J7R3AN/goomerbot/Redesign goomerbot/2020_520OB.SLDPRT

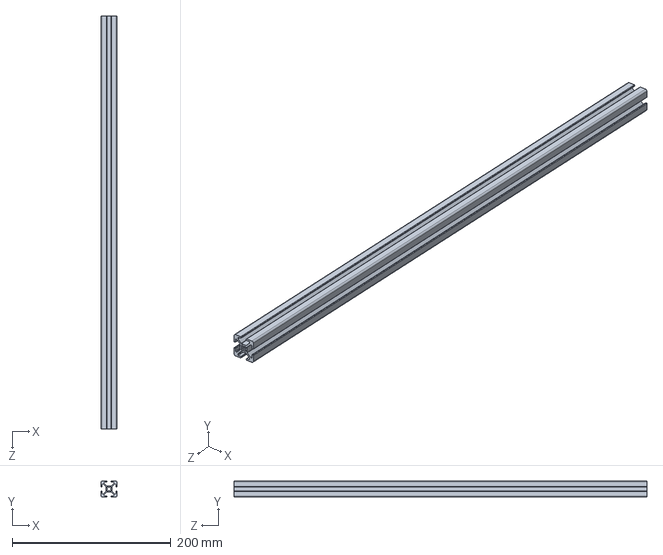
[picture p18: CAD file, 2017-09-06]
Redesign goomerbot/2020_520OB.SLDPRT
20.0 x 20.0 x 520.0 mm
