J7R3AN/goomerbot/Redesign goomerbot/2020_450OB.SLDPRT

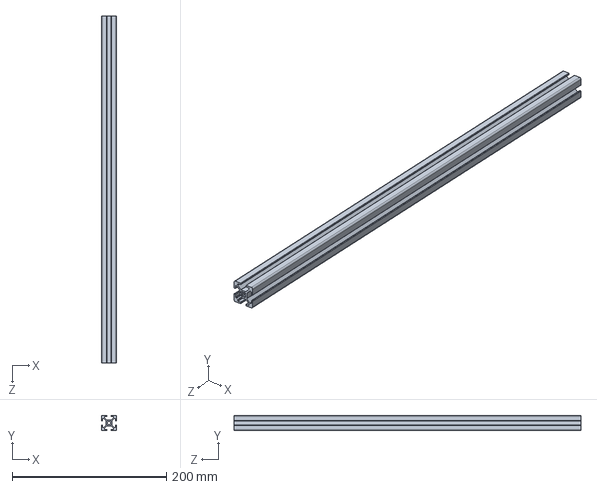
[picture p19: CAD file, 2017-09-06]
Redesign goomerbot/2020_450OB.SLDPRT
20.0 x 20.0 x 450.0 mm
