J7R3AN/goomerbot/SLDMODEL/Eje.SLDPRT

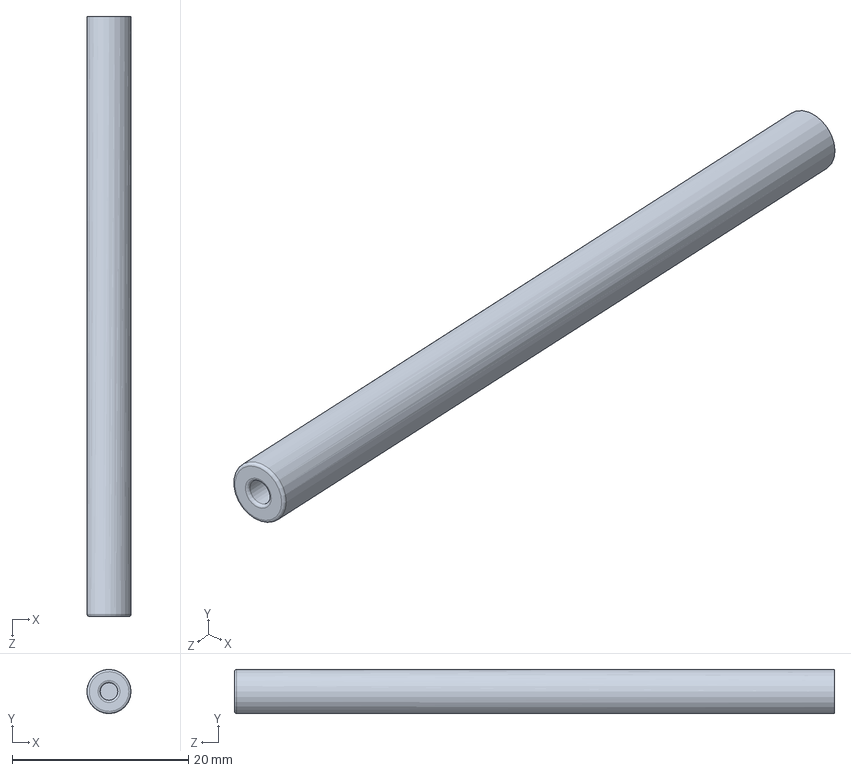
[picture p20: CAD file, 2017-03-24]
SLDMODEL/Eje.SLDPRT
5.00 x 5.00 x 68.0 mm
