J7R3AN/goomerbot/Redesign goomerbot/arduino-mega-mount.SLDPRT

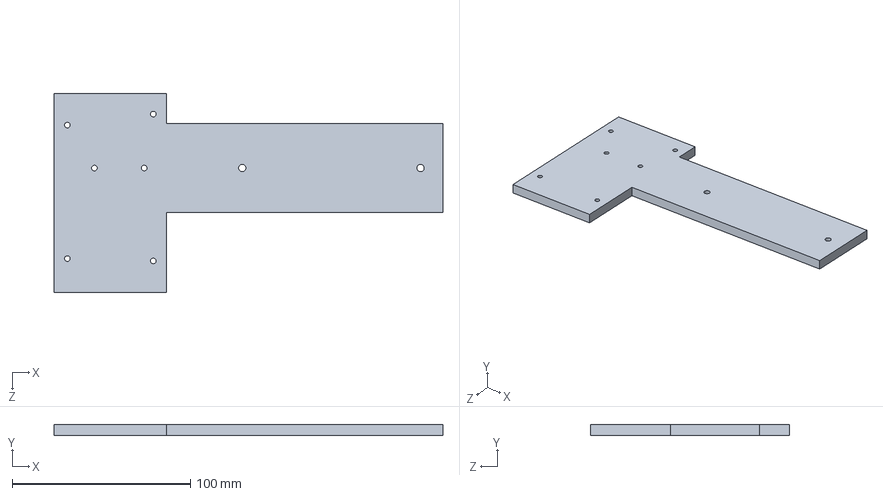
[picture p21: CAD file, 2017-09-06]
Redesign goomerbot/arduino-mega-mount.SLDPRT
218.2 x 6.35 x 111.6 mm
