J7R3AN/goomerbot/SLDMODEL/Cuerpo.SLDPRT

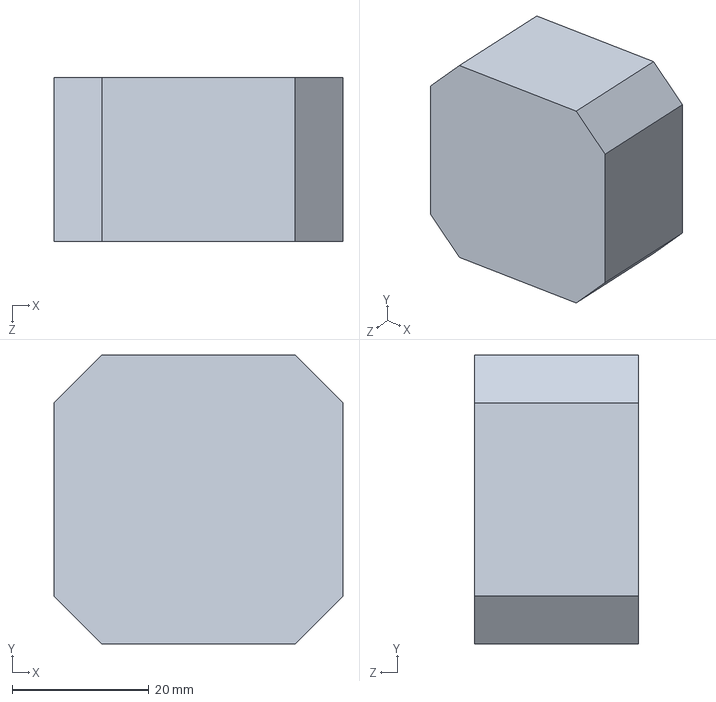
[picture p22: CAD file, 2017-03-24]
SLDMODEL/Cuerpo.SLDPRT
42.3 x 42.3 x 24.0 mm
