J7R3AN/goomerbot/SLDMODEL/2-belt pulley.SLDPRT

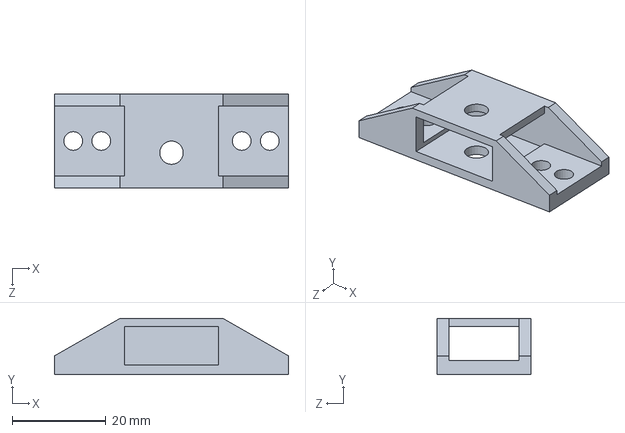
[picture p23: CAD file, 2017-03-24]
SLDMODEL/2-belt pulley.SLDPRT
50.0 x 12.0 x 20.0 mm
