J7R3AN/goomerbot/Redesign goomerbot/2X_single-bearing OB H-frame.STL

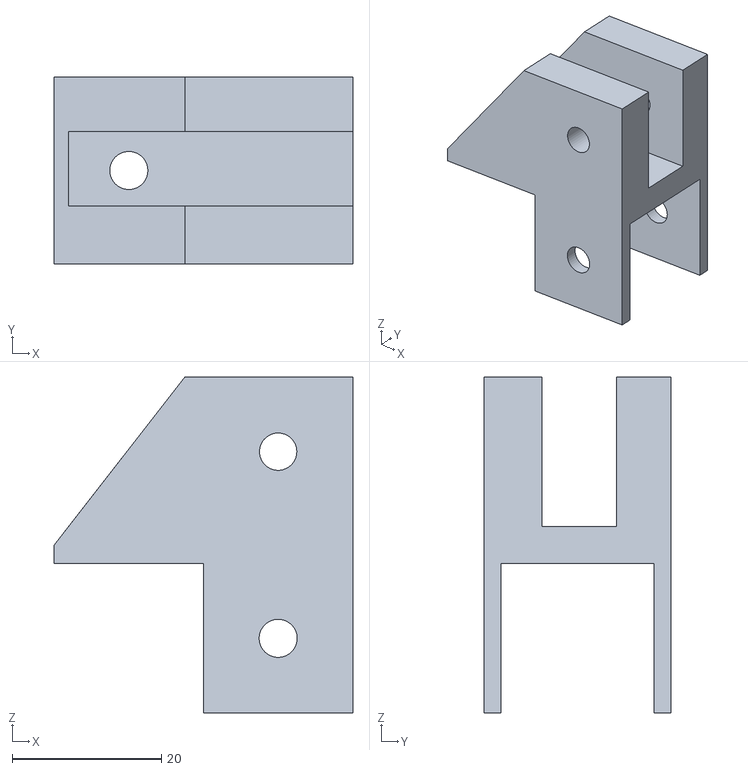
[picture p24: CAD file, 2017-09-06]
Redesign goomerbot/2X_single-bearing OB H-frame.STL
40.0 x 25.0 x 45.0
