J7R3AN/goomerbot/SLDMODEL/titan extruder.SLDPRT

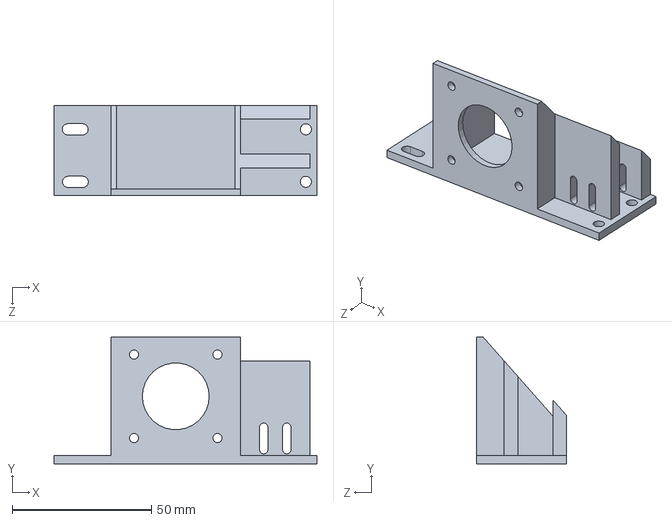
[picture p25: CAD file, 2017-03-24]
SLDMODEL/titan extruder.SLDPRT
94.5 x 45.5 x 32.5 mm
