J7R3AN/goomerbot/SLDMODEL/T5 Pulley.SLDPRT

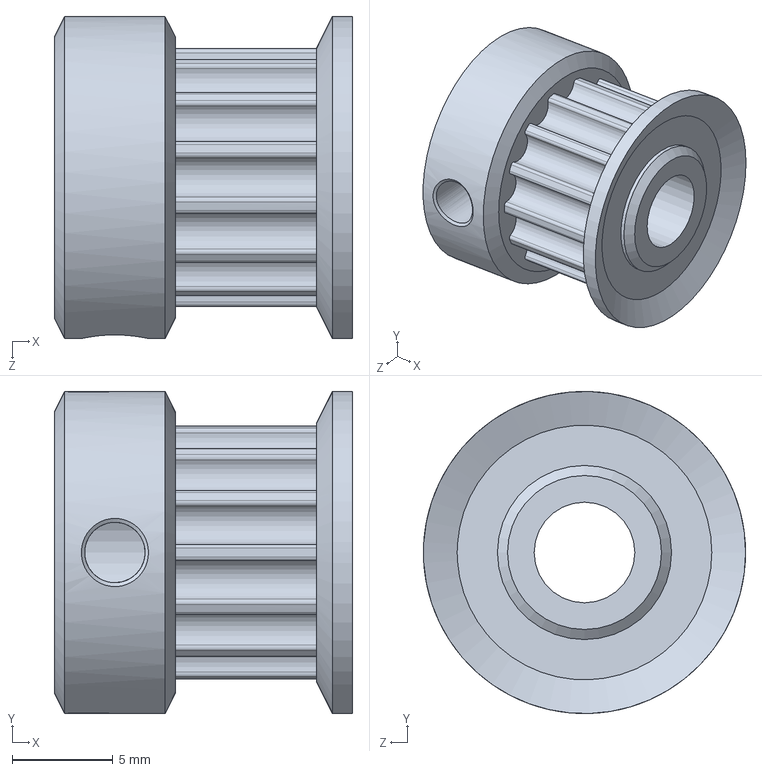
[picture p26: CAD file, 2017-03-24]
SLDMODEL/T5 Pulley.SLDPRT
14.8 x 16.0 x 16.0 mm
