J7R3AN/goomerbot/Redesign goomerbot/single-bearing OB H-frame.SLDPRT

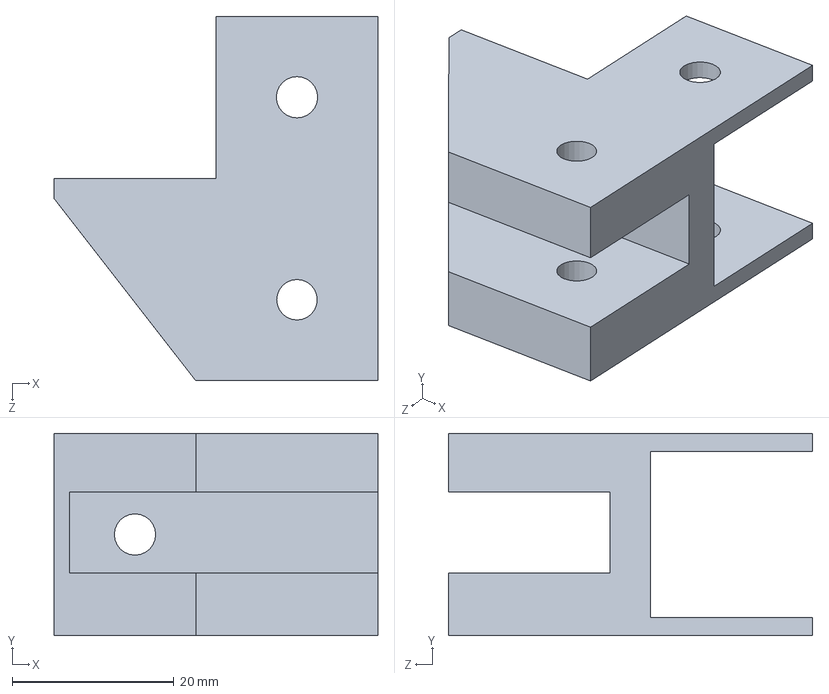
[picture p27: CAD file, 2017-08-04]
Redesign goomerbot/single-bearing OB H-frame.SLDPRT
40.0 x 25.0 x 45.0 mm
