J7R3AN/goomerbot/SLDMODEL/Tapa.SLDPRT

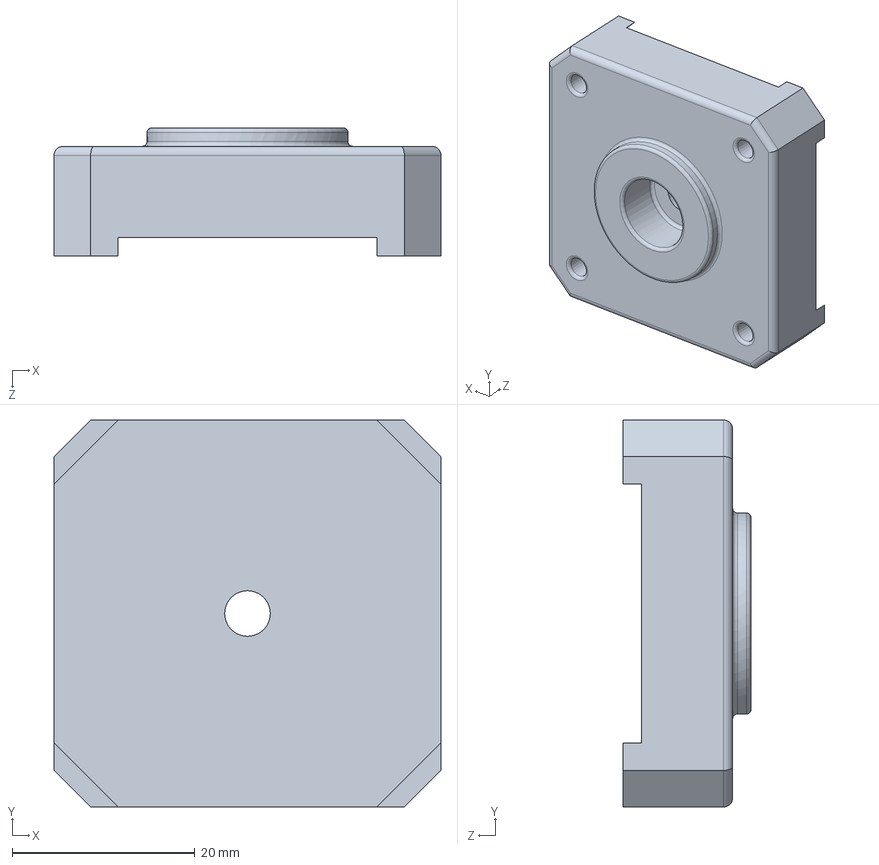
[picture p28: CAD file, 2017-01-27]
SLDMODEL/Tapa.SLDPRT
42.3 x 42.3 x 14.0 mm
