J7R3AN/goomerbot/SLDMODEL/Trapezoidal thread423mm.SLDPRT

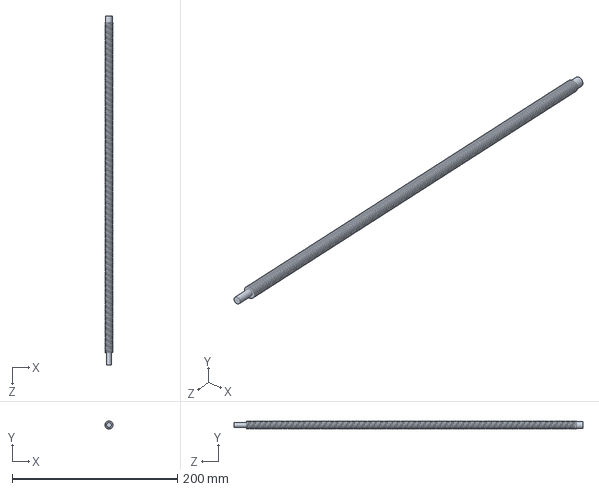
[picture p29: CAD file, 2017-01-27]
SLDMODEL/Trapezoidal thread423mm.SLDPRT
10.0 x 10.0 x 423.0 mm
