J7R3AN/goomerbot/Redesign goomerbot/200x300 build plate.SLDPRT

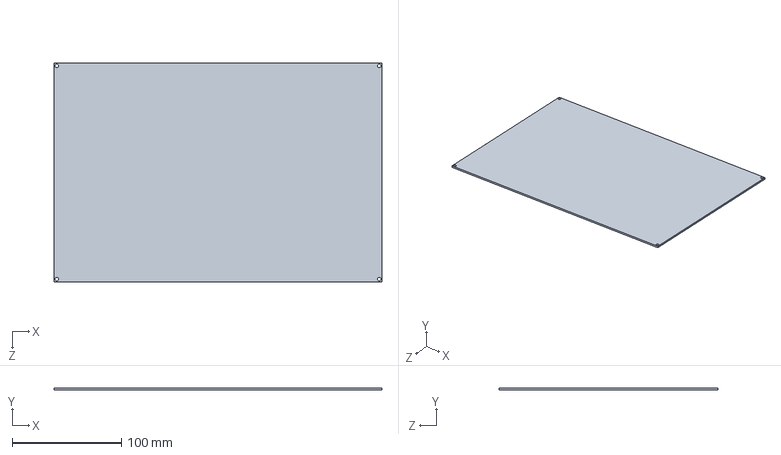
[picture p30: CAD file, 2017-01-27]
Redesign goomerbot/200x300 build plate.SLDPRT
300.0 x 2.00 x 200.0 mm
