J7R3AN/goomerbot/SLDMODEL/rod holder sk8.SLDPRT

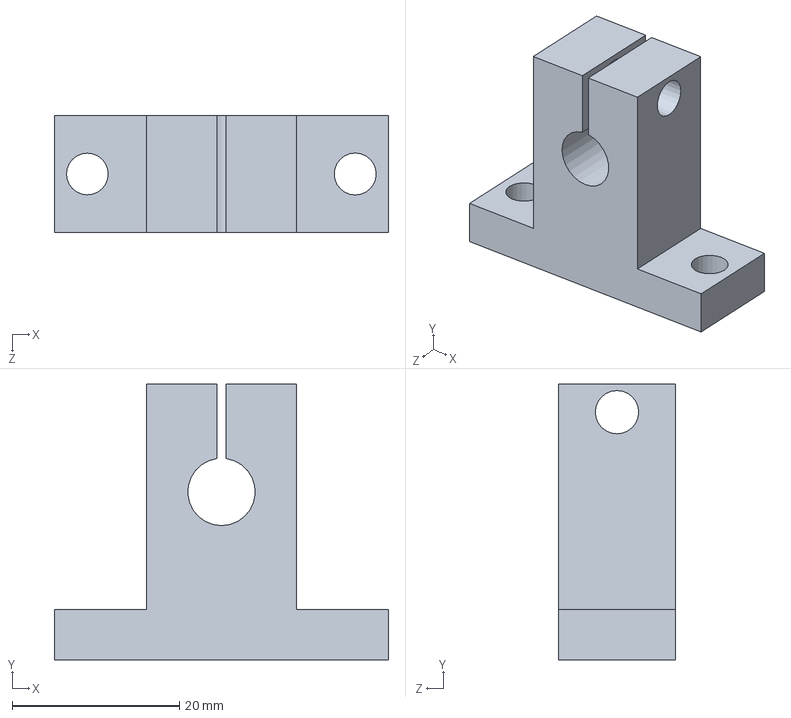
[picture p31: CAD file, 2017-01-27]
SLDMODEL/rod holder sk8.SLDPRT
40.0 x 33.0 x 14.0 mm
