J7R3AN/goomerbot/SLDMODEL/carriage to smooth rod H frame.SLDPRT

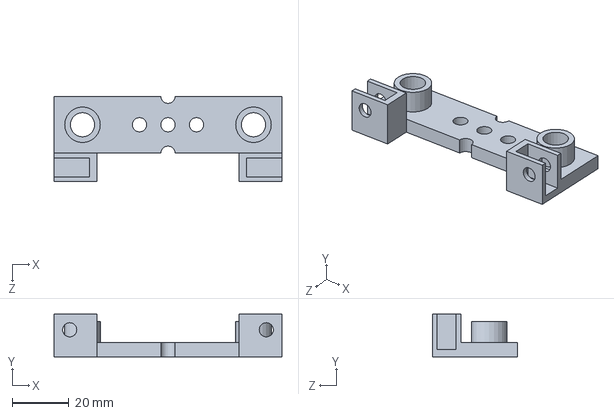
[picture p32: CAD file, 2017-01-27]
SLDMODEL/carriage to smooth rod H frame.SLDPRT
80.0 x 15.0 x 30.0 mm
