J7R3AN/goomerbot/Redesign goomerbot/linear bearings.SLDPRT

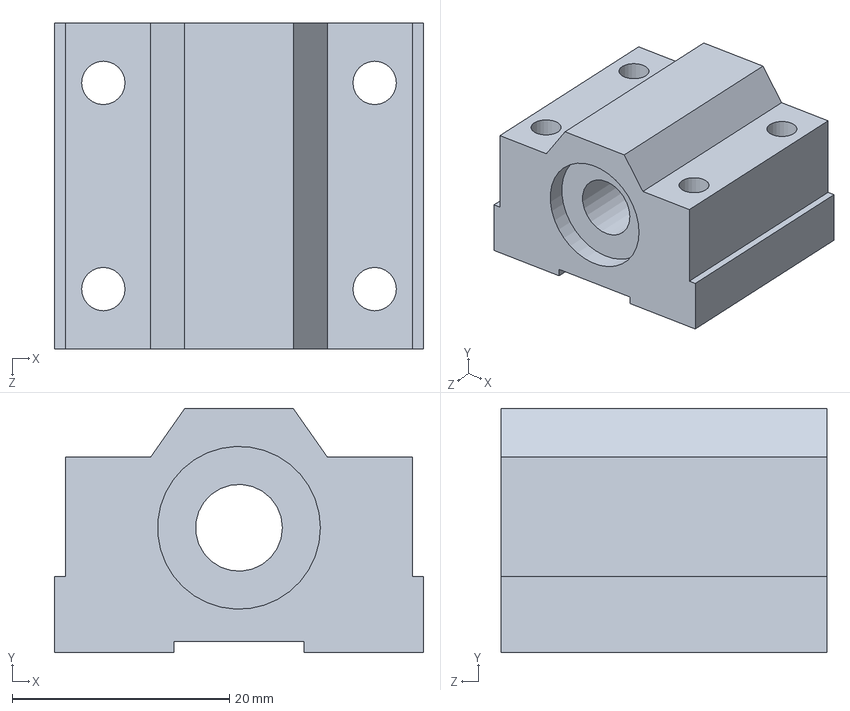
[picture p33: CAD file, 2017-01-27]
Redesign goomerbot/linear bearings.SLDPRT
34.0 x 22.5 x 30.0 mm
