J7R3AN/goomerbot/SLDMODEL/V6-BLOCK.SLDPRT

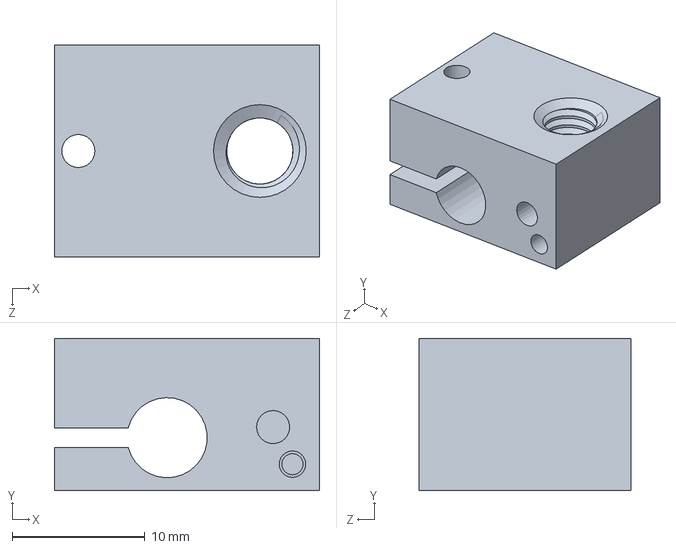
[picture p34: CAD file, 2017-01-27]
SLDMODEL/V6-BLOCK.SLDPRT
20.0 x 11.5 x 16.0 mm
