J7R3AN/goomerbot/Redesign goomerbot/smooth rod.SLDPRT

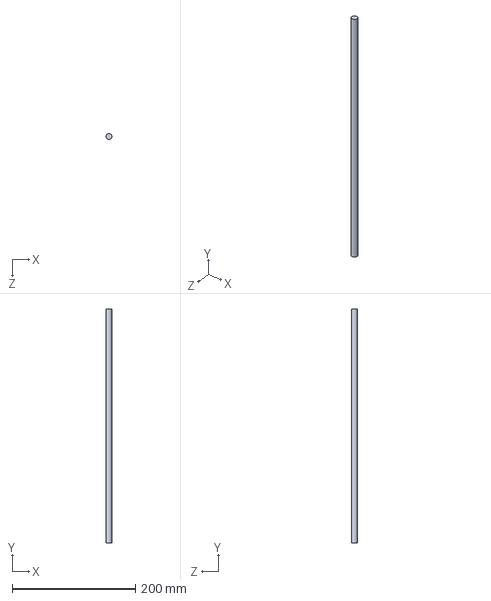
[picture p35: CAD file, 2017-01-27]
Redesign goomerbot/smooth rod.SLDPRT
9.53 x 380.0 x 9.53 mm
