J7R3AN/goomerbot/SLDMODEL/330-2020.SLDPRT

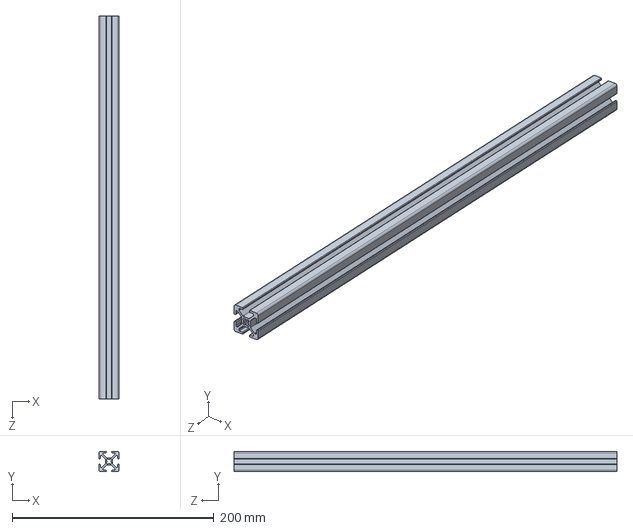
[picture p36: CAD file, 2017-01-27]
SLDMODEL/330-2020.SLDPRT
20.0 x 20.0 x 380.0 mm
