J7R3AN/goomerbot/Redesign goomerbot/Cast Corner Bracket.SLDPRT

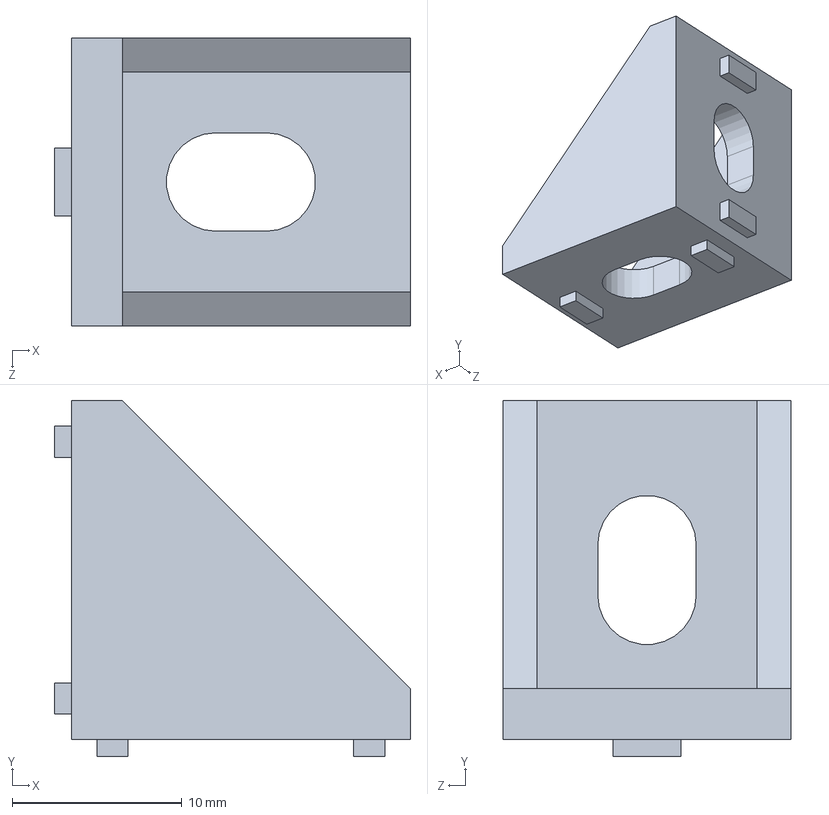
[picture p37: CAD file, 2017-01-27]
Redesign goomerbot/Cast Corner Bracket.SLDPRT
21.0 x 21.0 x 17.0 mm
