J7R3AN/goomerbot/SLDMODEL/V6-175-BREAK.SLDPRT

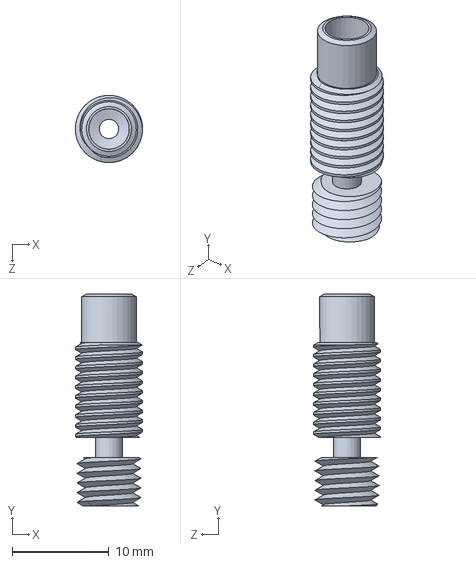
[picture p38: CAD file, 2017-01-27]
SLDMODEL/V6-175-BREAK.SLDPRT
6.95 x 21.9 x 6.95 mm
