J7R3AN/goomerbot/SLDMODEL/Xtreme Mini V Wheel.SLDPRT

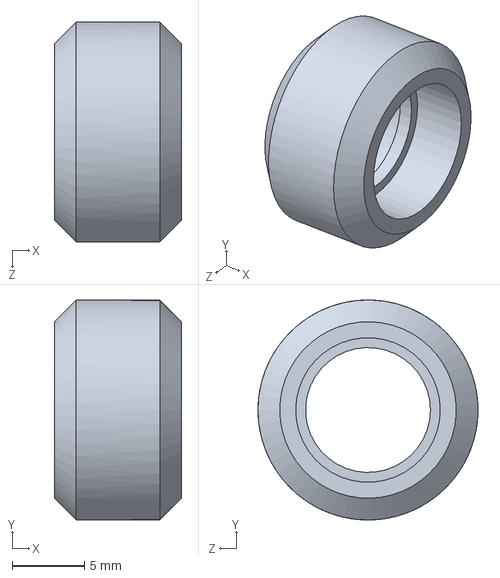
[picture p39: CAD file, 2017-01-27]
SLDMODEL/Xtreme Mini V Wheel.SLDPRT
8.80 x 15.2 x 15.2 mm
