J7R3AN/goomerbot/SLDMODEL/metal L bracket.SLDPRT

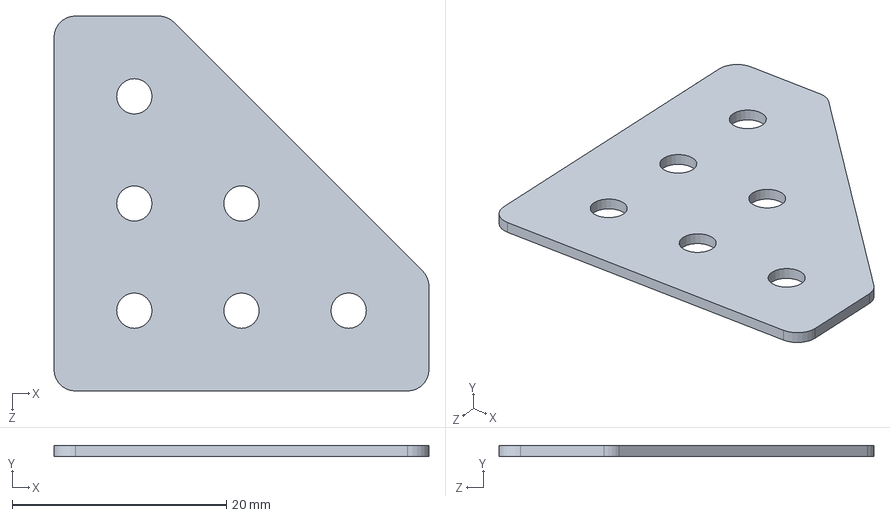
[picture p40: CAD file, 2017-01-27]
SLDMODEL/metal L bracket.SLDPRT
35.0 x 1.00 x 35.0 mm
