J7R3AN/goomerbot/SLDMODEL/Aluminum Spacer 6mm.SLDPRT

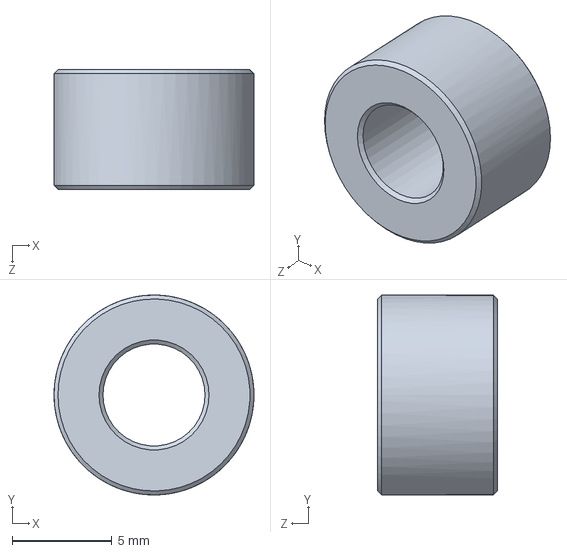
[picture p41: CAD file, 2017-01-27]
SLDMODEL/Aluminum Spacer 6mm.SLDPRT
10.0 x 10.00 x 6.00 mm
