J7R3AN/goomerbot/SLDMODEL/V6-NOZZLE-175-035.SLDPRT

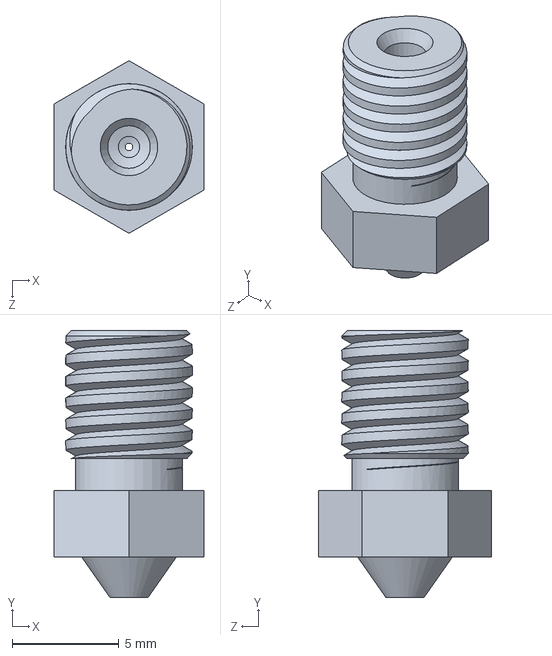
[picture p42: CAD file, 2017-01-27]
SLDMODEL/V6-NOZZLE-175-035.SLDPRT
7.00 x 12.5 x 8.08 mm
