J7R3AN/goomerbot/SLDMODEL/Unviersal Carriage.SLDPRT

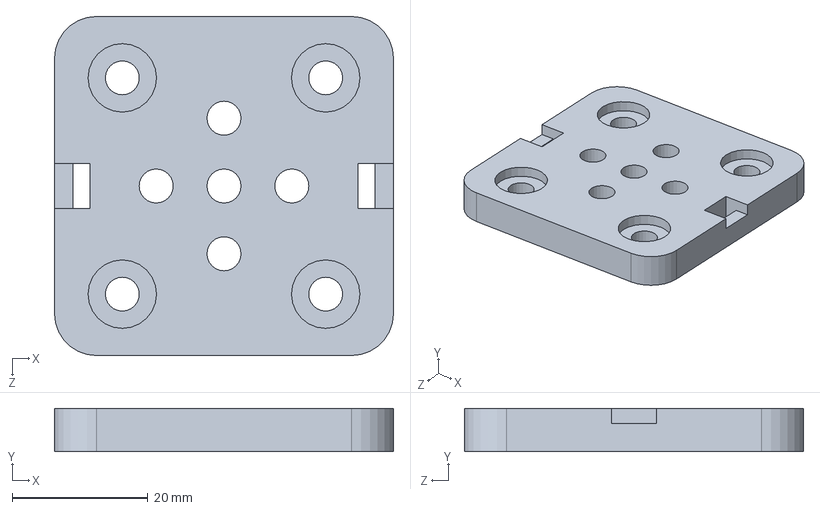
[picture p43: CAD file, 2017-01-27]
SLDMODEL/Unviersal Carriage.SLDPRT
50.0 x 6.35 x 50.0 mm
