J7R3AN/goomerbot/SLDMODEL/V6-175-SINK.SLDPRT

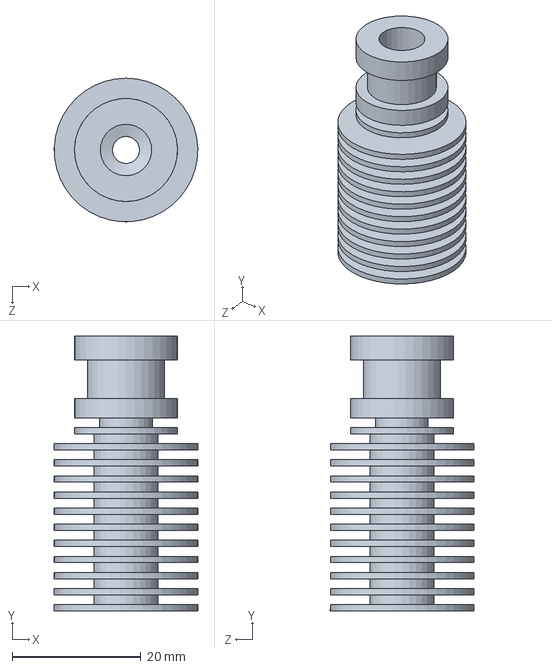
[picture p44: CAD file, 2017-01-27]
SLDMODEL/V6-175-SINK.SLDPRT
22.3 x 42.7 x 22.3 mm
