J7R3AN/goomerbot/SLDMODEL/350-2020.SLDPRT

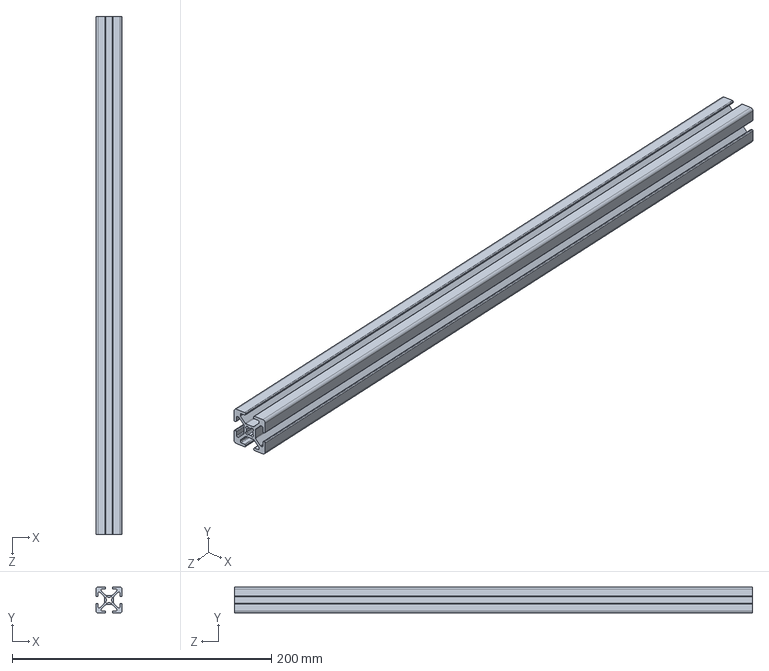
[picture p45: CAD file, 2017-01-27]
SLDMODEL/350-2020.SLDPRT
20.0 x 20.0 x 400.0 mm
