J7R3AN/goomerbot/SLDMODEL/motormounts.SLDPRT

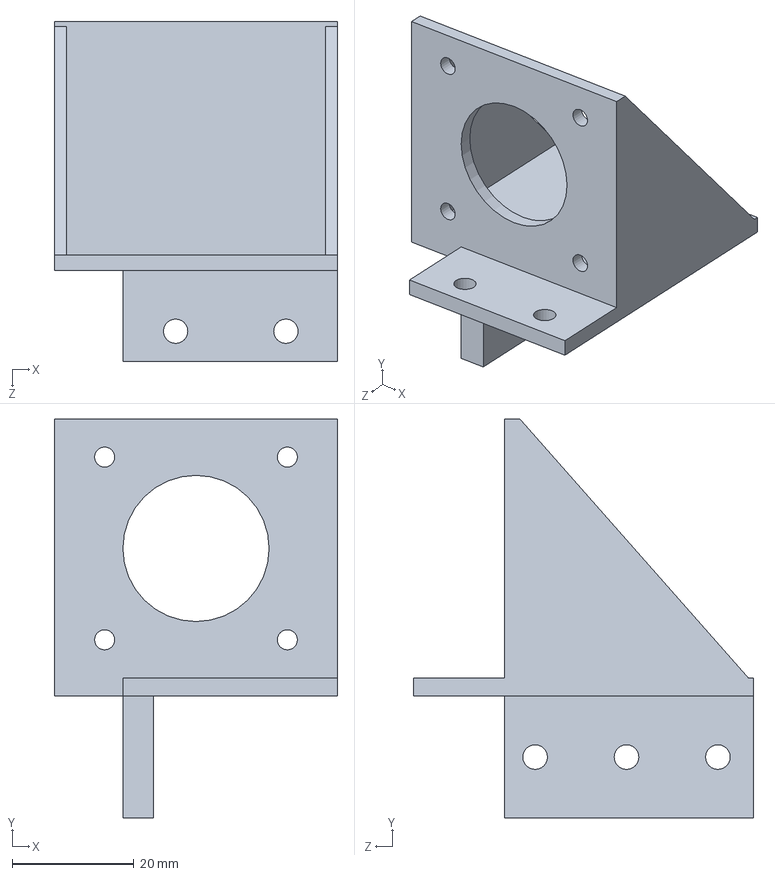
[picture p46: CAD file, 2017-01-27]
SLDMODEL/motormounts.SLDPRT
46.5 x 65.5 x 55.9 mm
