J7R3AN/goomerbot/SLDMODEL/motormountsmirrored.SLDPRT

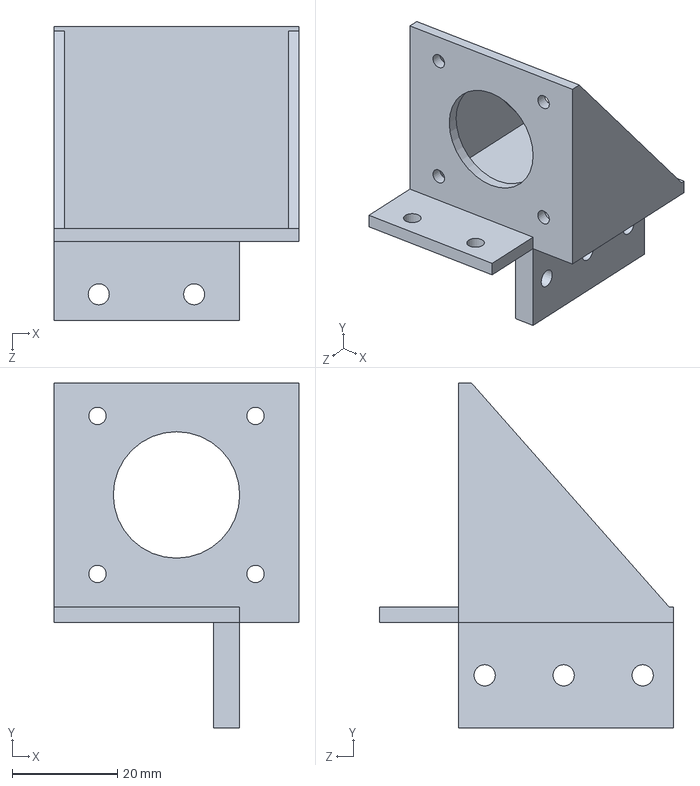
[picture p47: CAD file, 2017-01-27]
SLDMODEL/motormountsmirrored.SLDPRT
46.5 x 65.5 x 55.9 mm
