J7R3AN/goomerbot/SLDMODEL/Ball Bearing 5 x 10 x 4.2.SLDPRT

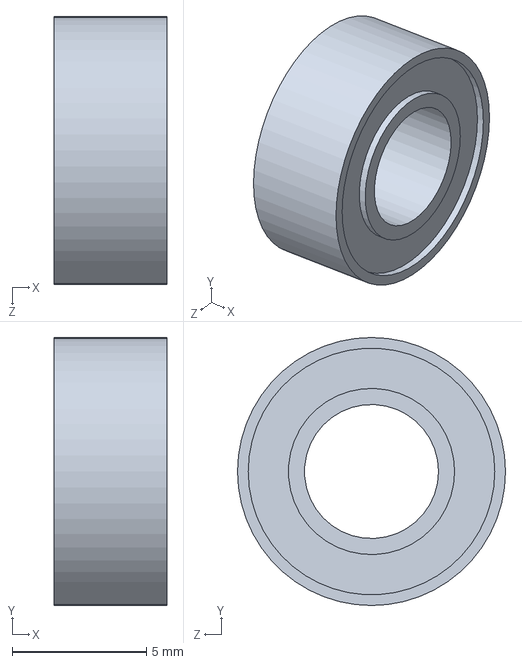
[picture p48: CAD file, 2017-01-27]
SLDMODEL/Ball Bearing 5 x 10 x 4.2.SLDPRT
4.20 x 10.0 x 10.0 mm
