J7R3AN/goomerbot/SLDMODEL/Base.SLDPRT

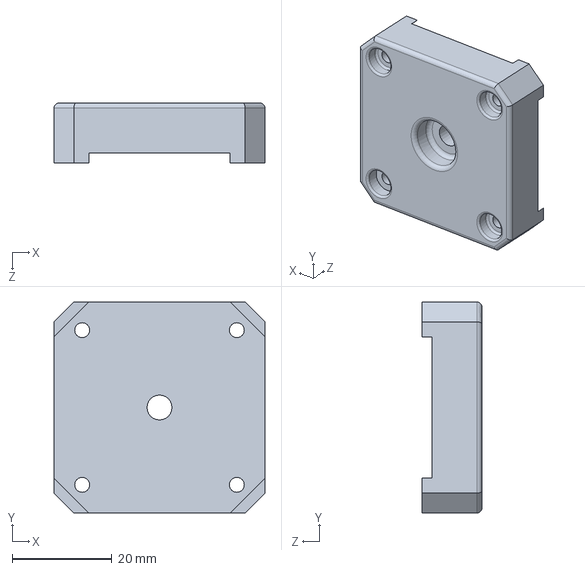
[picture p49: CAD file, 2017-01-27]
SLDMODEL/Base.SLDPRT
42.3 x 42.3 x 12.0 mm
